rgnazar/FIREGOTO-firmware/FIREGOTO/Boards/PlacaWEB_etch_silk_bottom.pdf

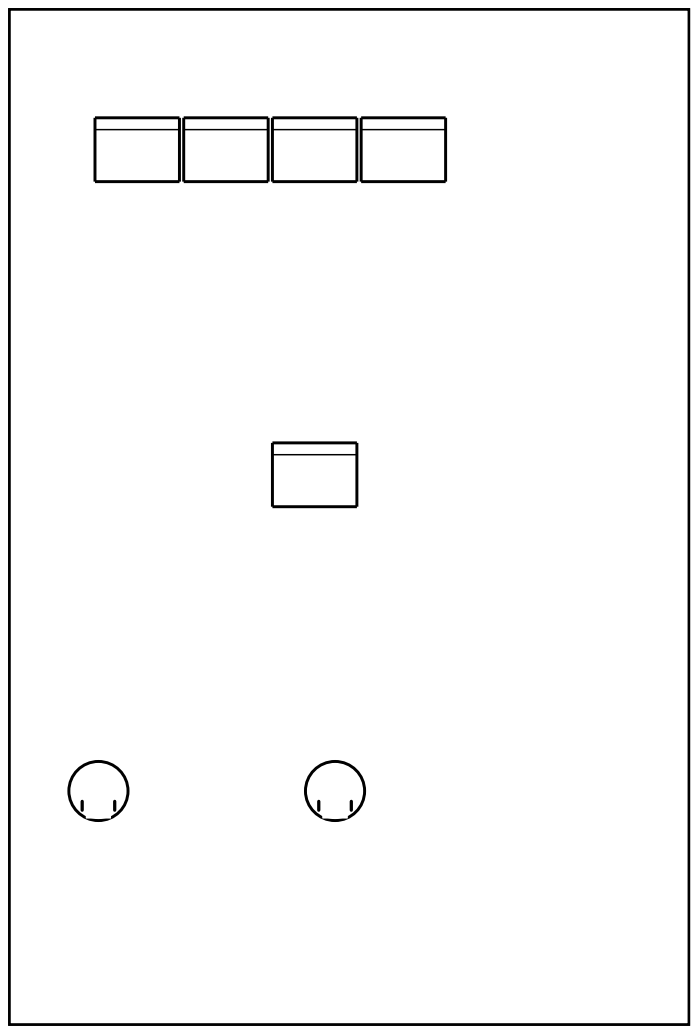
[picture p7: page 1]
