rgnazar/FIREGOTO-firmware/FIREGOTO/Boards/PlacaWEB_etch_silk_bottom_mirror.pdf

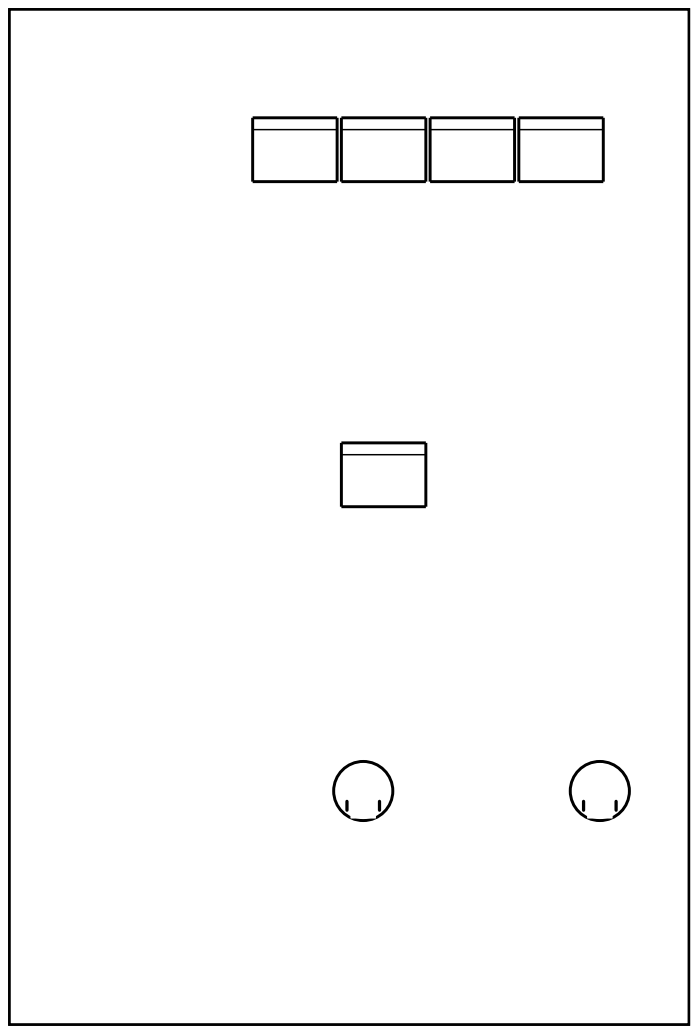
[picture p8: page 1]
