rgnazar/FIREGOTO-firmware/FIREGOTO/Boards/PlacaWEB_etch_silk_top.pdf

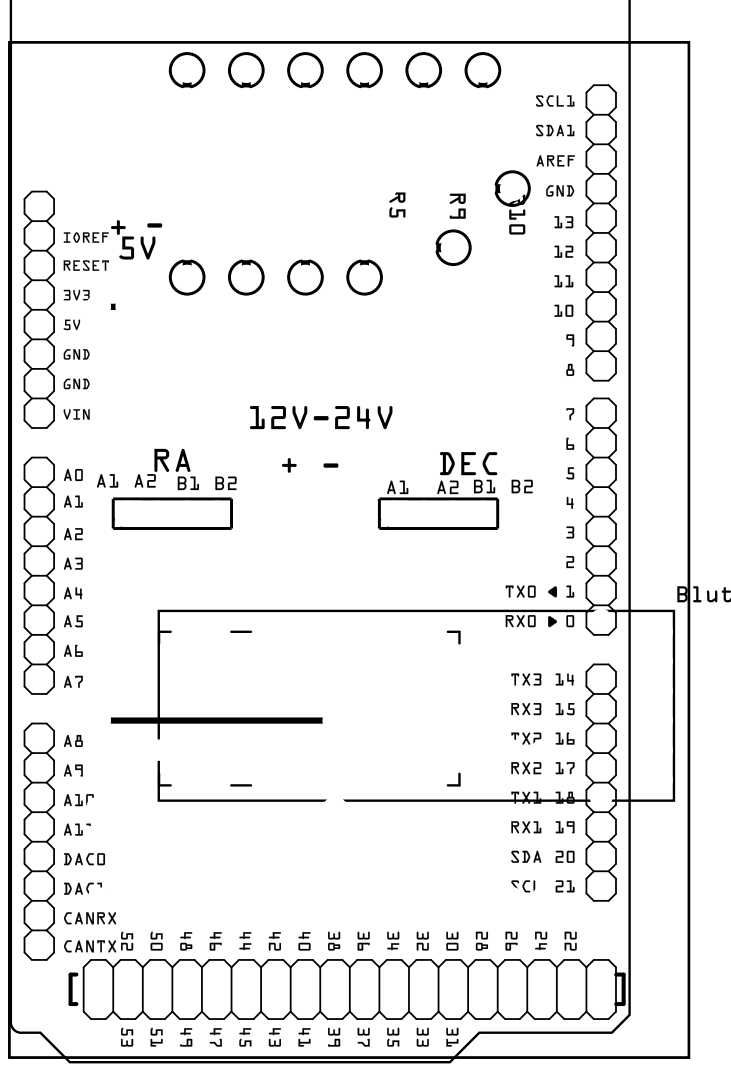
[picture p9: page 1]
