rgnazar/FIREGOTO-firmware/FIREGOTO/Boards/PlacaWEB_etch_silk_top_mirror.pdf

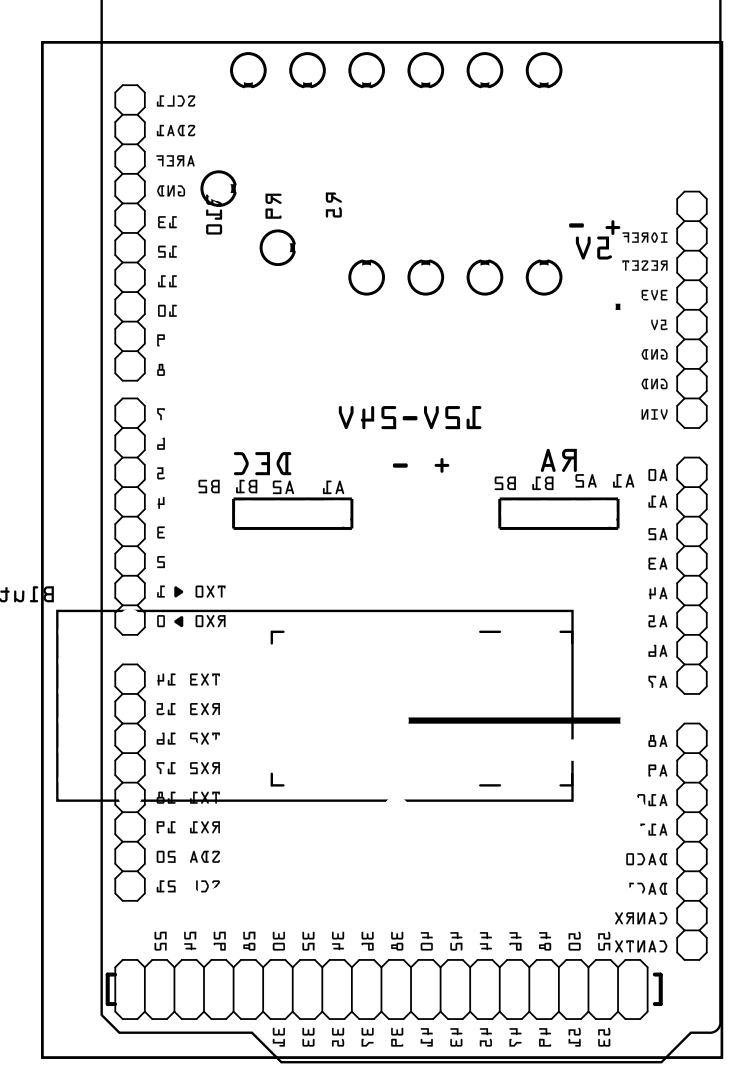
[picture p10: page 1]
